JordanAceto/Phasor_II/front_panel/docs/html_nav/images/cat_pcb_top_jpg_panel_front.png

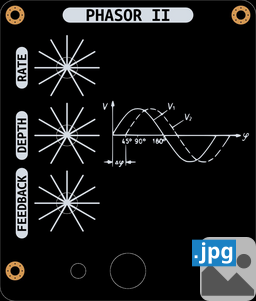
front_panel/docs/html_nav/images/cat_pcb_top_jpg_panel_front.png
