JordanAceto/Phasor_II/main_pcb/docs/html_nav/images/cat_pcb_bottom_jpg_phasor_II-bottom.png

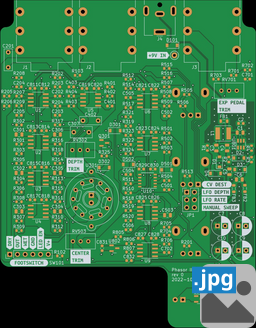
main_pcb/docs/html_nav/images/cat_pcb_bottom_jpg_phasor_II-bottom.png
