JordanAceto/Phasor_II/main_pcb/docs/html_nav/images/cat_PCB_phasor_II-F_Cu.png

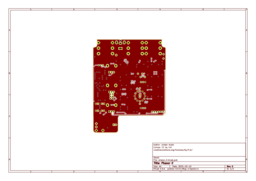
main_pcb/docs/html_nav/images/cat_PCB_phasor_II-F_Cu.png
