JordanAceto/Phasor_II/main_pcb/docs/html_nav/images/cat_pcb_top_jpg_phasor_II-top.png

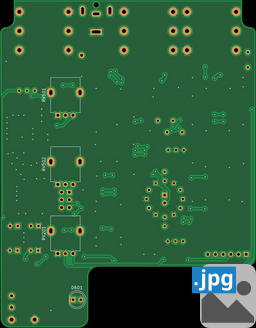
main_pcb/docs/html_nav/images/cat_pcb_top_jpg_phasor_II-top.png
