JordanAceto/Phasor_II/main_pcb/docs/html_nav/images/cat_pdf_layers_phasor_II-B_Courtyard.png

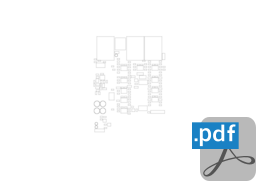
main_pcb/docs/html_nav/images/cat_pdf_layers_phasor_II-B_Courtyard.png
