JordanAceto/Phasor_II/pics/front.JPG

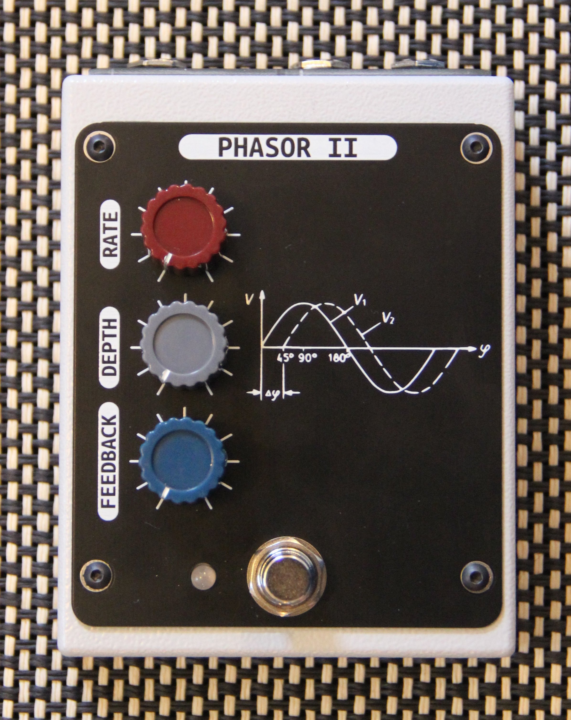
pics/front.JPG
