JordanAceto/Phasor_II/pics/jacks.JPG

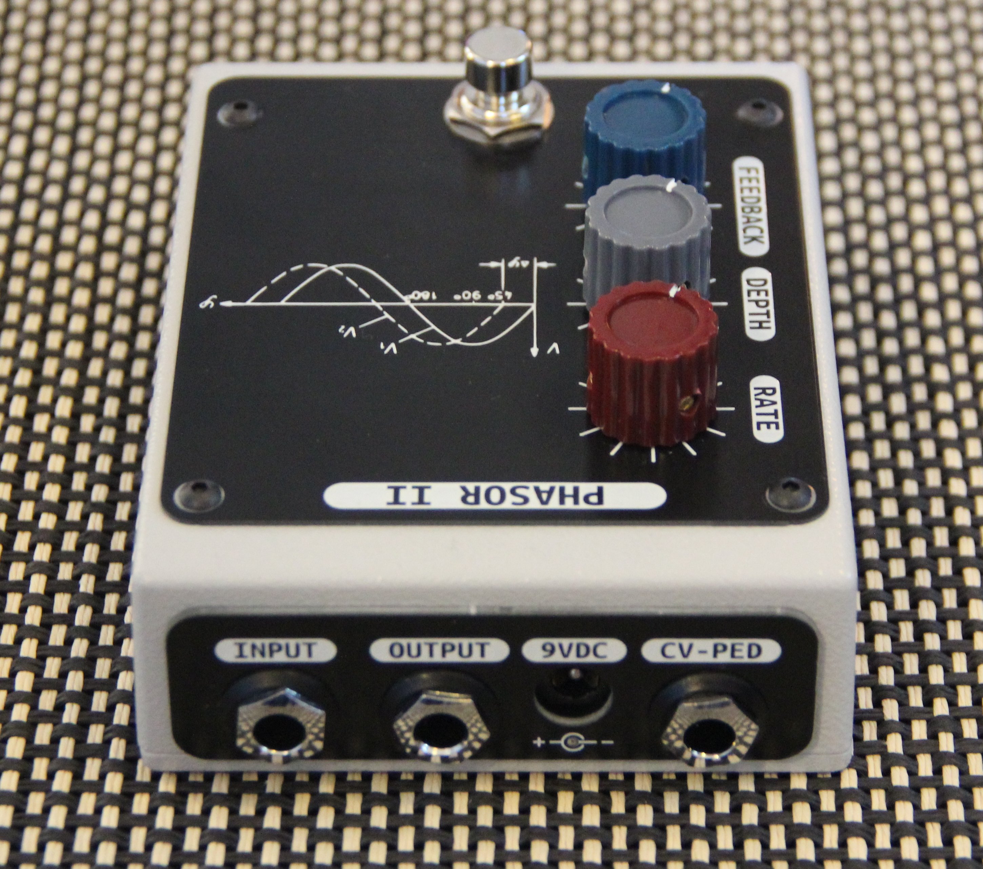
pics/jacks.JPG
