JordanAceto/Phasor_II/main_pcb/docs/html_nav/images/cat_pdf_sch_print_phasor_II-schematic.png

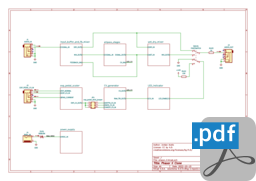
main_pcb/docs/html_nav/images/cat_pdf_sch_print_phasor_II-schematic.png
