JordanAceto/Phasor_II/main_pcb/docs/2D/individual_layers/phasor_II-F_Mask.pdf

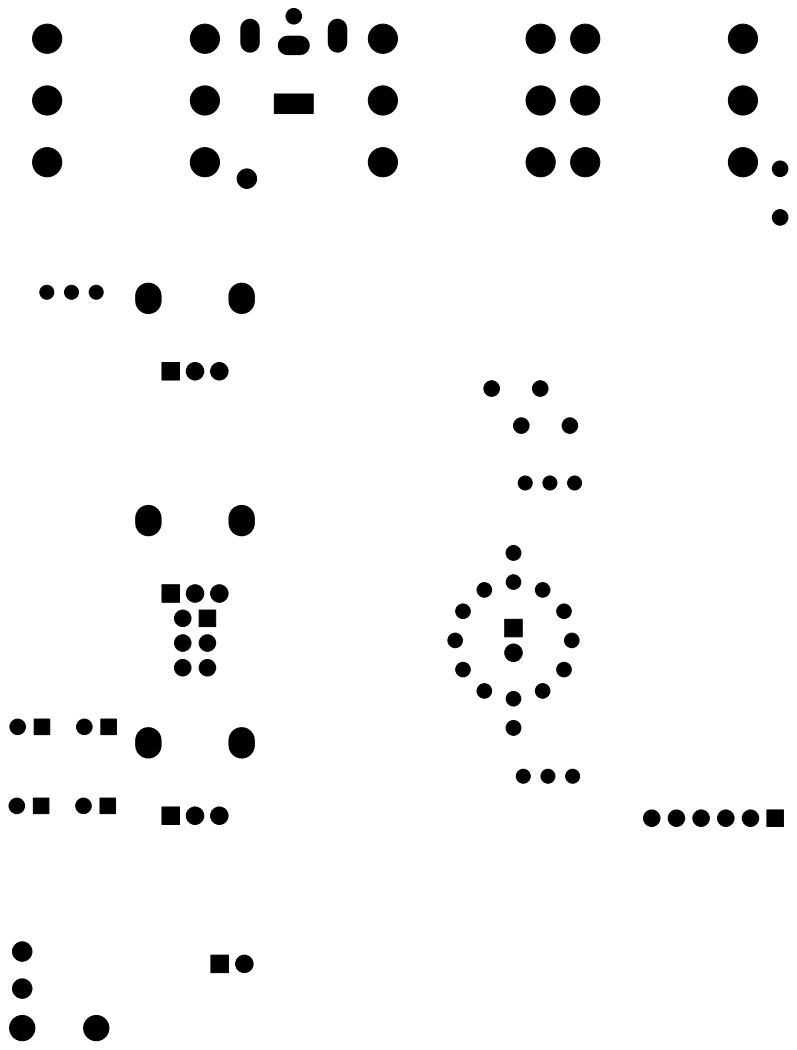
[picture p45: page 1]
