JordanAceto/Phasor_II/main_pcb/docs/2D/individual_layers/phasor_II-F_Silkscreen.pdf

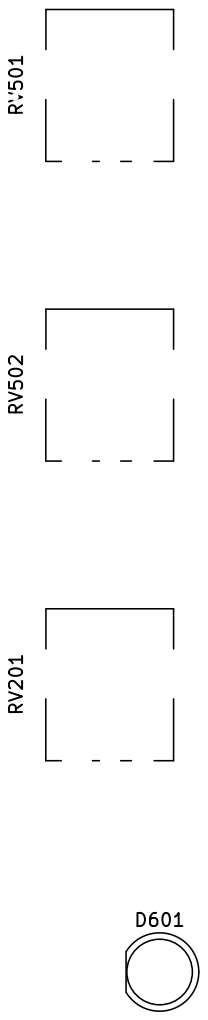
[picture p46: page 1]
